zekearneodo/squintan32/altium_libraries/Microdrive_Drive/3d_footprints/sql-rv-1.8-6-body.STEP

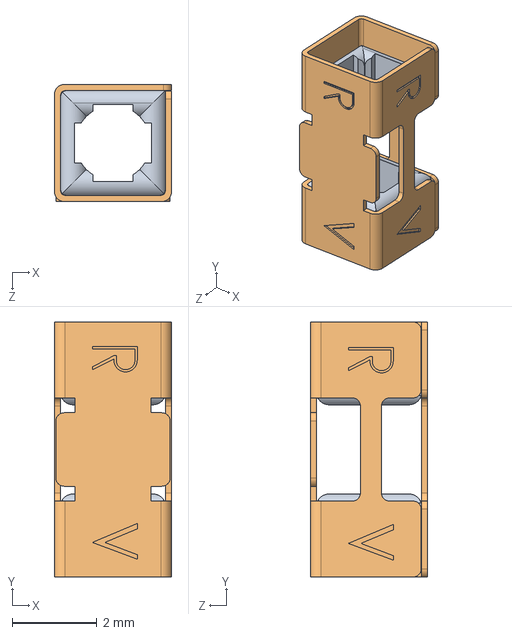
[picture p12: CAD file, 2020-01-03]
altium_libraries/Microdrive_Drive/3d_footprints/sql-rv-1.8-6-body.STEP
2.77 x 6.02 x 2.77 mm
02559-0-0000_WRAPPED x 2
02915-0-0000_Correct Wrap
