zekearneodo/squintan32/altium_libraries/RHD2000_eval_board/3dmodels/pcb_connector_852-10-036-20-001101.stp

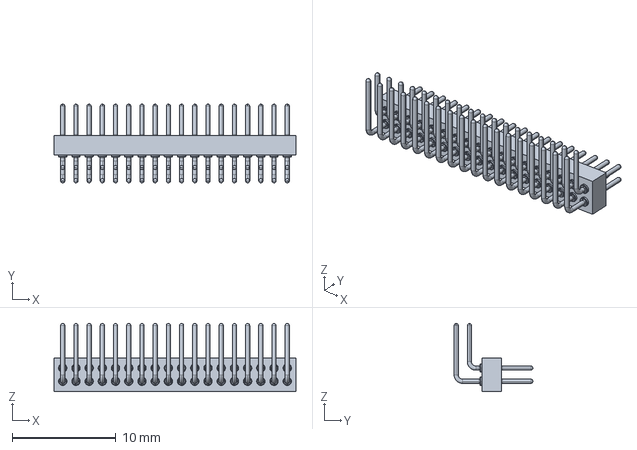
[picture p13: CAD file, 2020-01-03]
altium_libraries/RHD2000_eval_board/3dmodels/pcb_connector_852-10-036-20-001101.stp
23.3 x 7.58 x 6.55 mm
