zekearneodo/squintan32/rev_1_mechanic/pcstl/rhd_board_rev1_right_rules_copy.step

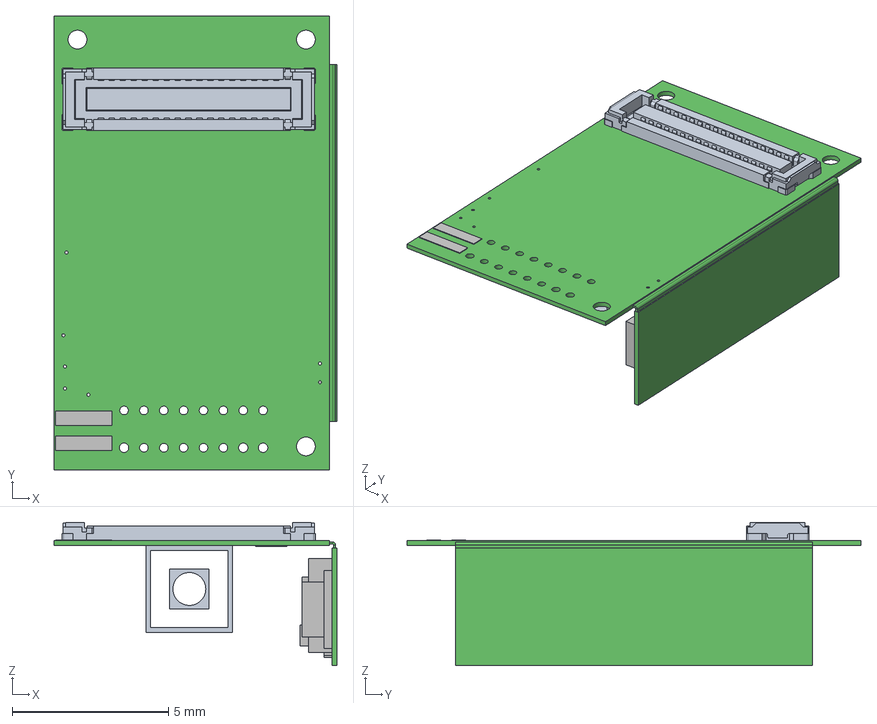
[picture p14: CAD file, 2020-01-03]
rev_1_mechanic/pcstl/rhd_board_rev1_right_rules_copy.step
9.04 x 14.5 x 4.57 mm
Board
sql-rv-1.8-6-12_nc
Extruded x 49
