zekearneodo/squintan32/rev_1_mechanic/stl/shuttle_female_slider.STEP

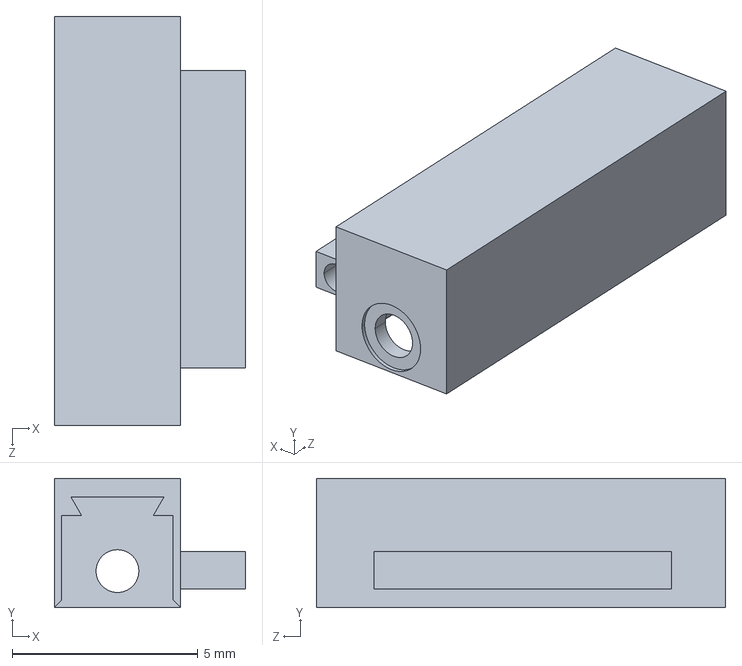
[picture p15: CAD file, 2020-01-03]
rev_1_mechanic/stl/shuttle_female_slider.STEP
5.15 x 3.47 x 11.0 mm
