zekearneodo/squintan32/rhd2132_with_squiggle_logic/mechanical/board_rev0.SLDPRT

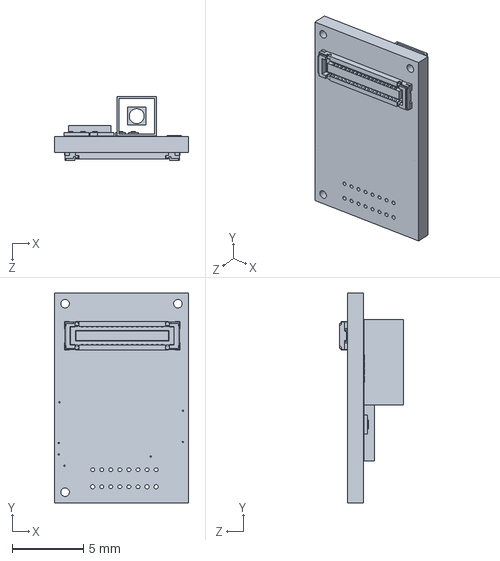
[picture p16: CAD file, 2020-01-03]
rhd2132_with_squiggle_logic/mechanical/board_rev0.SLDPRT
9.40 x 14.7 x 4.50 mm
