zekearneodo/squintan32/rhd2132_with_squiggle_logic/mechanical/rev_1/board_rv1.SLDPRT

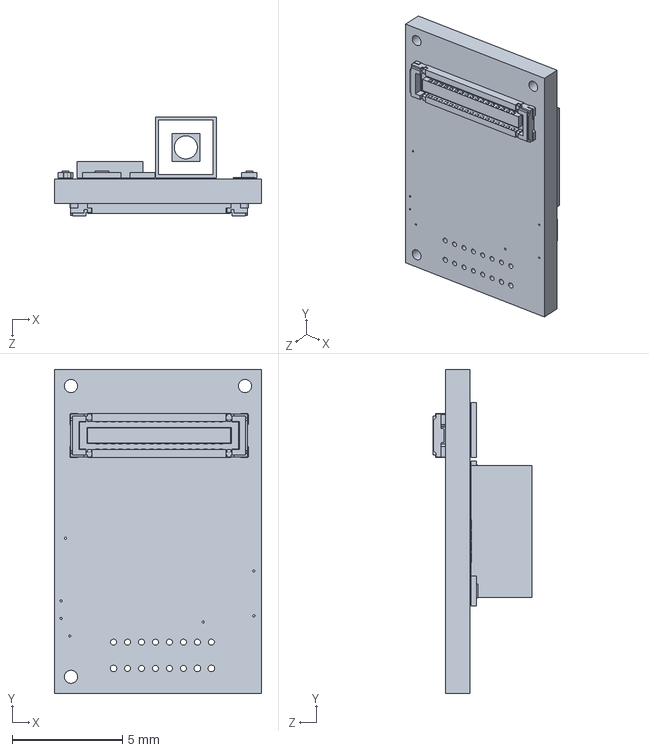
[picture p17: CAD file, 2020-01-03]
rhd2132_with_squiggle_logic/mechanical/rev_1/board_rv1.SLDPRT
9.40 x 14.7 x 4.50 mm
