zekearneodo/squintan32/rhd2132_with_squiggle_logic/Project Outputs for rhd_board/K111027/ExportSTEP/rhd_board_rev1_2.step

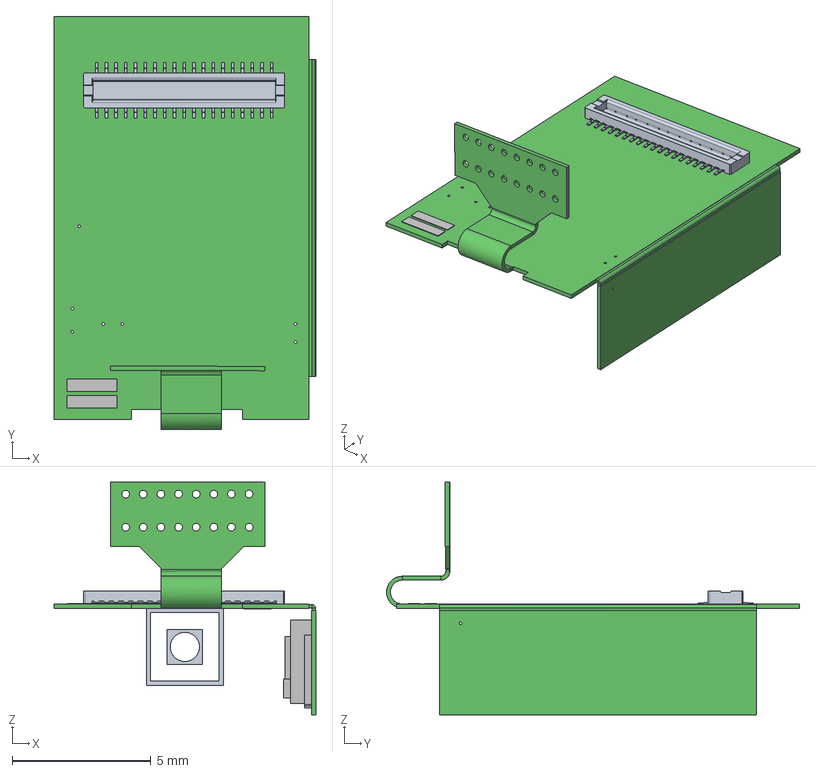
[picture p18: CAD file, 2020-01-03]
rhd2132_with_squiggle_logic/Project Outputs for rhd_board/K111027/ExportSTEP/rhd_board_rev1_2.step
9.43 x 14.9 x 8.38 mm
Board
sql-rv-1.8-6-12_nc
Extruded x 48
