zekearneodo/squintan32/rev_1_mechanic/pcstl/rhd_board_rev1_right_ruless_375hallpy.SLDPRT

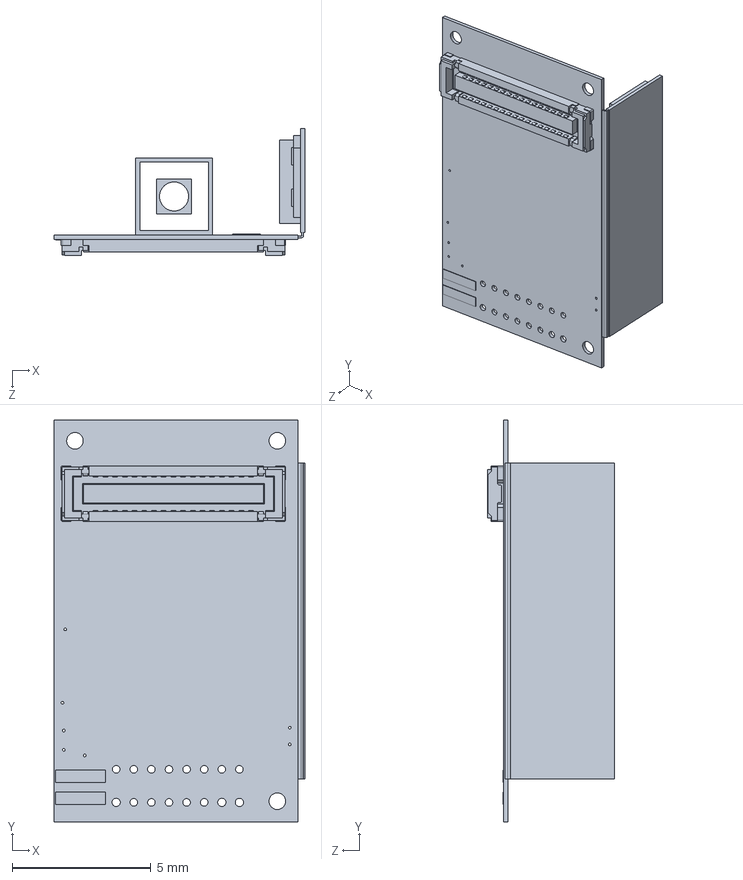
[picture p19: CAD file, 2020-01-03]
rev_1_mechanic/pcstl/rhd_board_rev1_right_ruless_375hallpy.SLDPRT
9.04 x 14.5 x 4.57 mm
