zekearneodo/squintan32/rev_1_mechanic/stl/frame.STEP

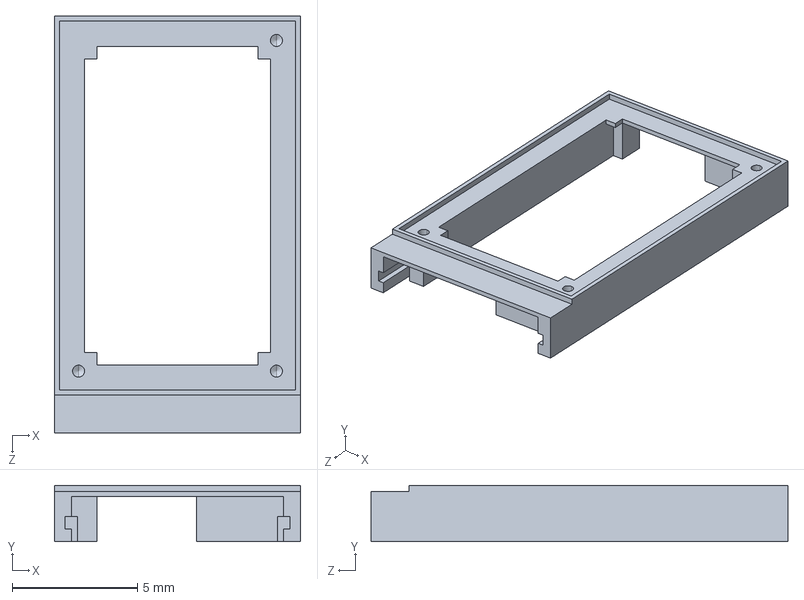
[picture p20: CAD file, 2020-01-03]
rev_1_mechanic/stl/frame.STEP
9.82 x 2.25 x 16.6 mm
