zekearneodo/squintan32/rev_1_mechanic/stl/derived_slider_female.STEP

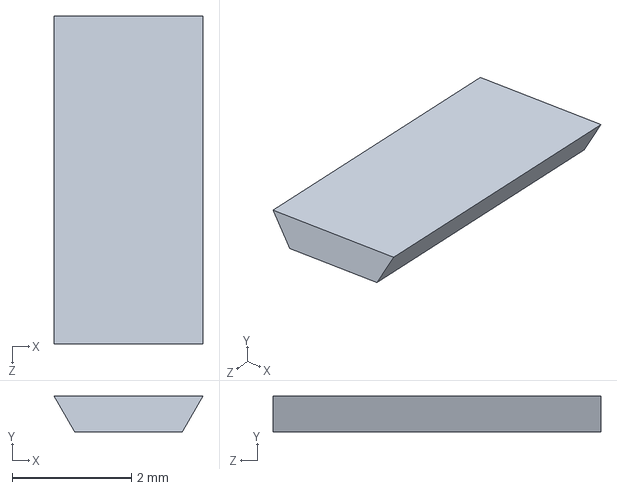
[picture p21: CAD file, 2020-01-03]
rev_1_mechanic/stl/derived_slider_female.STEP
2.50 x 0.6 x 5.50 mm
