zekearneodo/squintan32/rhd2132_with_squiggle_logic/mechanical/rhd_board_rev1.step

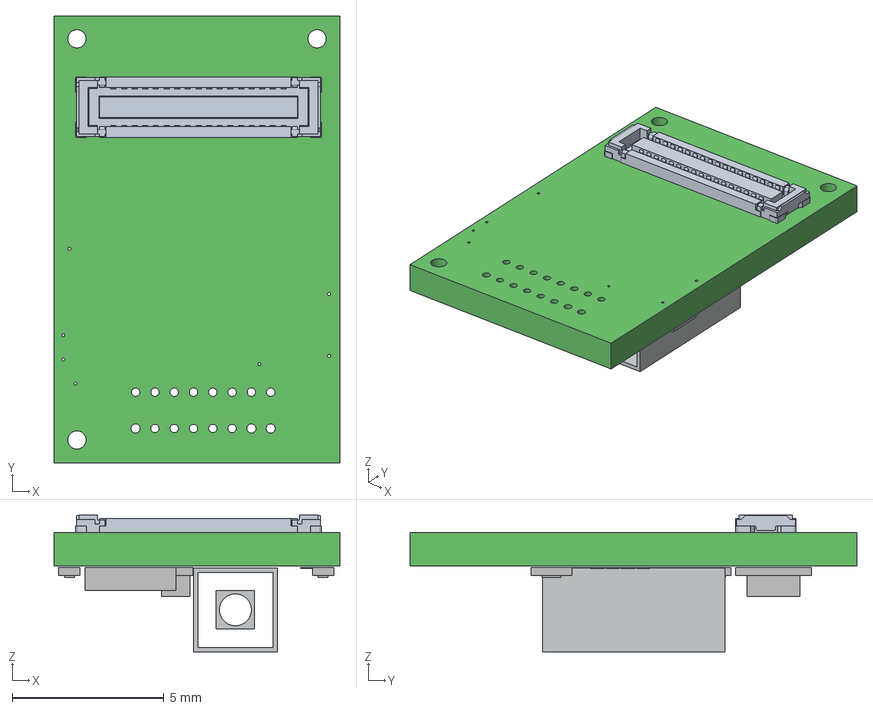
[picture p22: CAD file, 2020-01-03]
rhd2132_with_squiggle_logic/mechanical/rhd_board_rev1.step
9.40 x 14.7 x 4.50 mm
Board
piezo_actuator x 2
Extruded x 47
PS-
PS+
C1
