zekearneodo/squintan32/rev_1_mechanic/stl/shuttle_cap.STEP

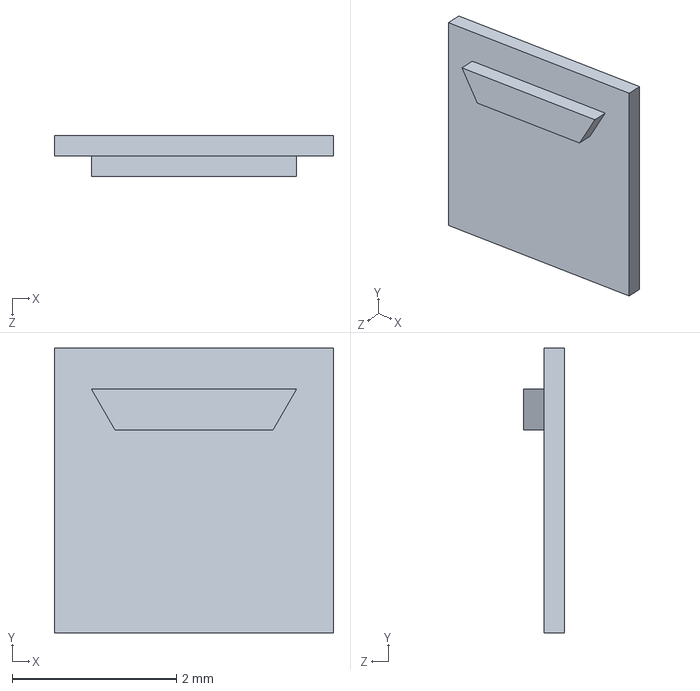
[picture p23: CAD file, 2020-01-03]
rev_1_mechanic/stl/shuttle_cap.STEP
3.40 x 3.47 x 0.5 mm
