zekearneodo/squintan32/altium_libraries/Microdrive_Drive/3d_footprints/sql-rv-1.8-6-12_nc.STEP

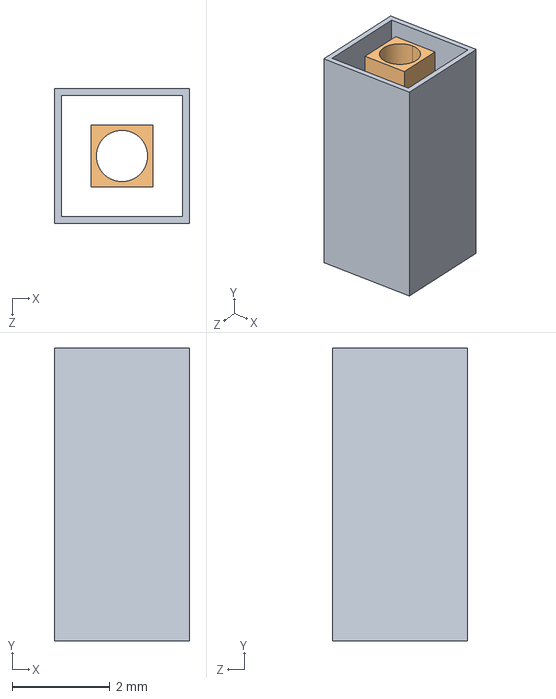
[picture p25: CAD file, 2020-01-03]
altium_libraries/Microdrive_Drive/3d_footprints/sql-rv-1.8-6-12_nc.STEP
2.77 x 6.00 x 2.77 mm
