zekearneodo/squintan32/rev_1_mechanic/stl/case.STEP

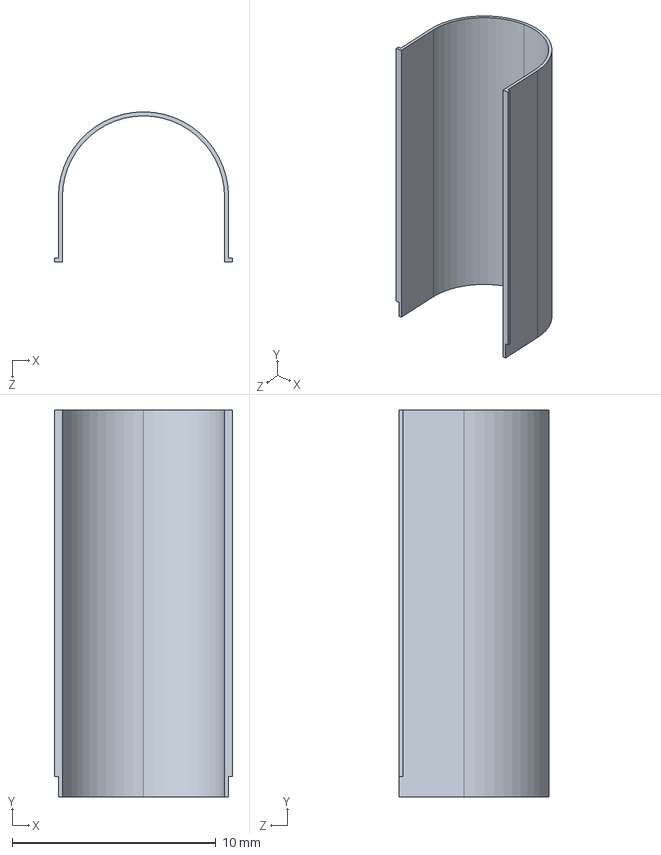
[picture p26: CAD file, 2020-01-03]
rev_1_mechanic/stl/case.STEP
8.76 x 19.0 x 7.38 mm
