zekearneodo/squintan32/rhd2132_with_squiggle_logic/mechanical/omnetics_pzn16_dd.STEP

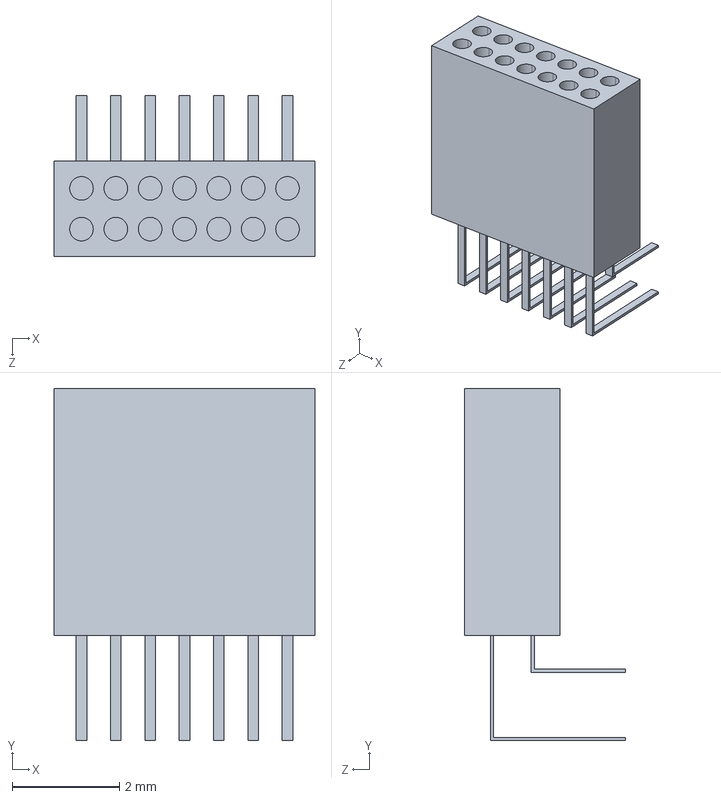
[picture p27: CAD file, 2020-01-03]
rhd2132_with_squiggle_logic/mechanical/omnetics_pzn16_dd.STEP
4.86 x 6.56 x 3.00 mm
