zekearneodo/squintan32/rhd2132_with_squiggle_logic/output_3d_model/board_folded.SLDPRT

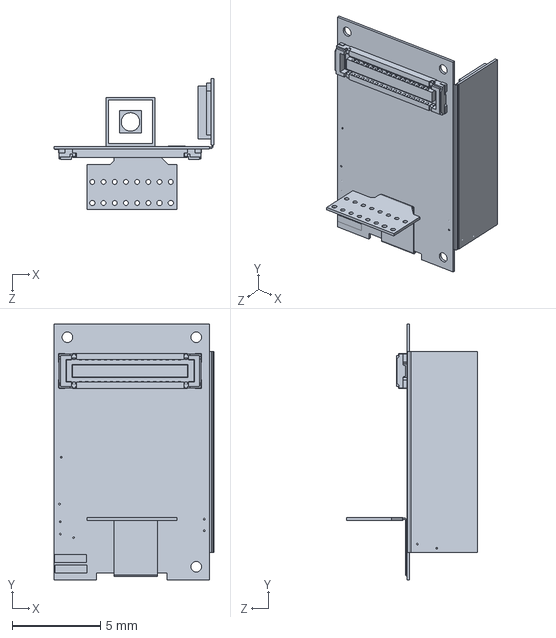
[picture p28: CAD file, 2020-01-03]
rhd2132_with_squiggle_logic/output_3d_model/board_folded.SLDPRT
9.04 x 14.5 x 7.40 mm
