zekearneodo/squintan32/rhd2132_with_squiggle_logic/mechanical/Copy of rhd_board.step

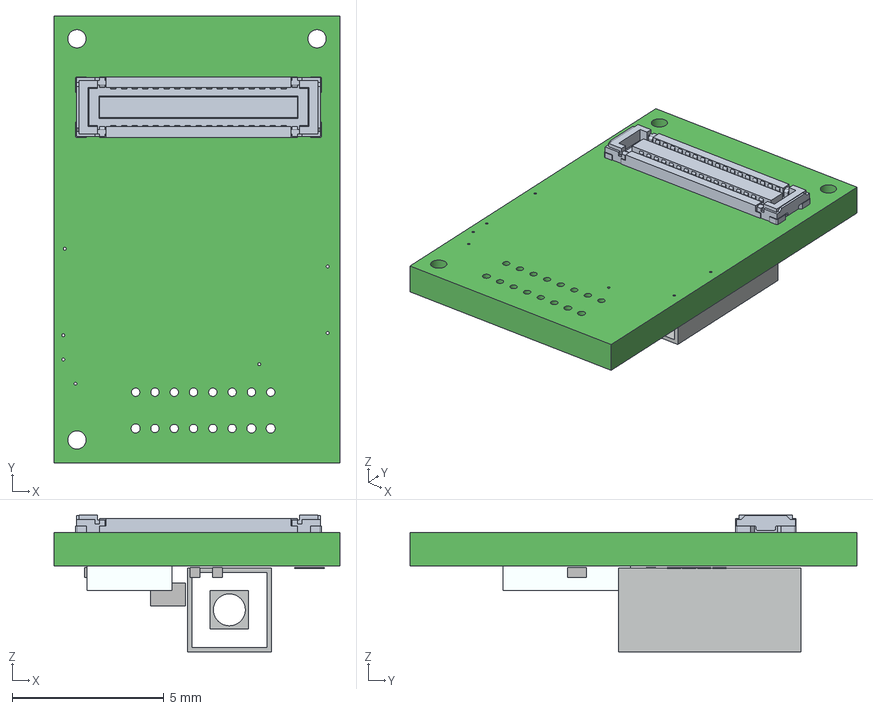
[picture p29: CAD file, 2020-01-03]
rhd2132_with_squiggle_logic/mechanical/Copy of rhd_board.step
9.40 x 14.7 x 4.50 mm
Board
piezo_actuator x 2
Extruded x 13
U0
PS-
PS+
