zekearneodo/squintan32/rev_1_mechanic/cap.SLDPRT

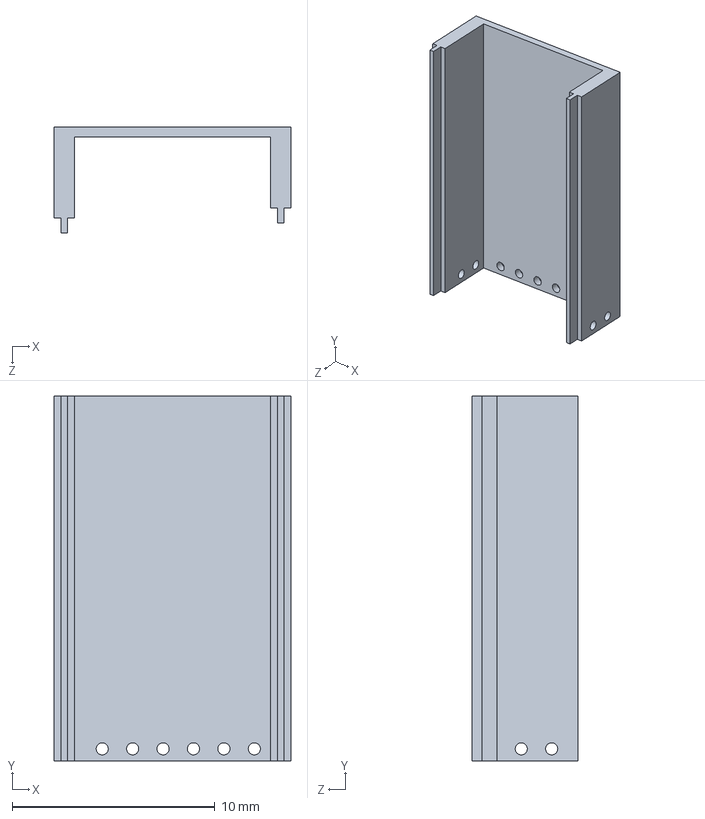
[picture p30: CAD file, 2020-01-03]
rev_1_mechanic/cap.SLDPRT
11.7 x 18.0 x 5.25 mm
