zekearneodo/squintan32/rev_1_mechanic/Magnet_S.SLDPRT

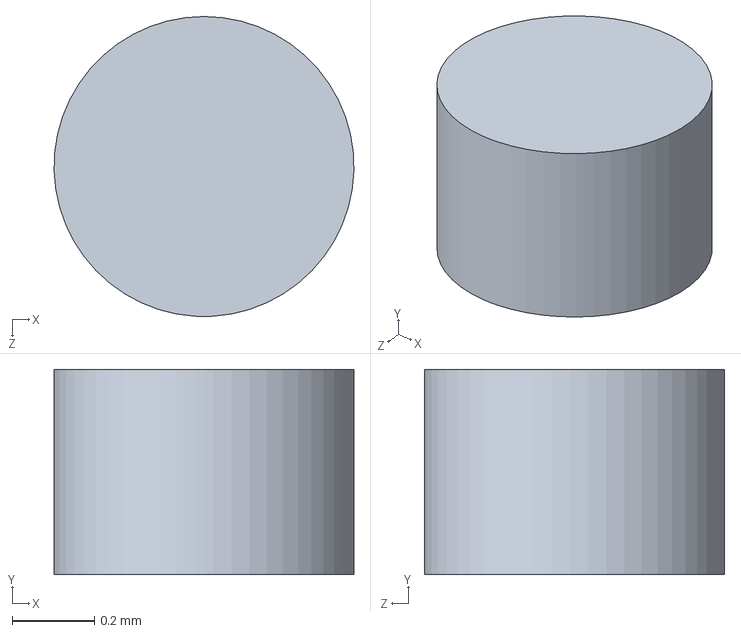
[picture p31: CAD file, 2020-01-03]
rev_1_mechanic/Magnet_S.SLDPRT
0.73 x 0.5 x 0.73 mm
