zekearneodo/squintan32/rev_1_mechanic/slider_derived_male.SLDPRT

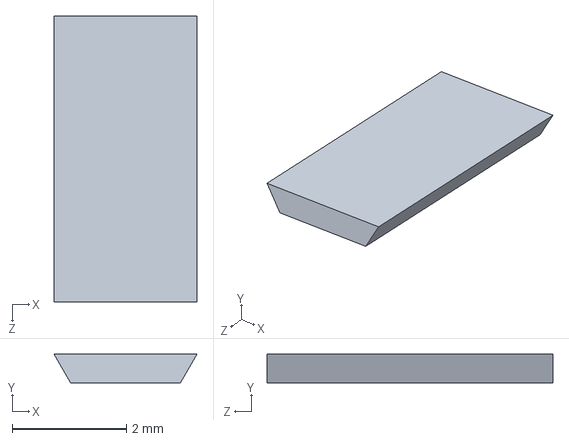
[picture p32: CAD file, 2020-01-03]
rev_1_mechanic/slider_derived_male.SLDPRT
2.50 x 0.5 x 5.00 mm
