zekearneodo/squintan32/rev_1_mechanic/shaft.SLDPRT

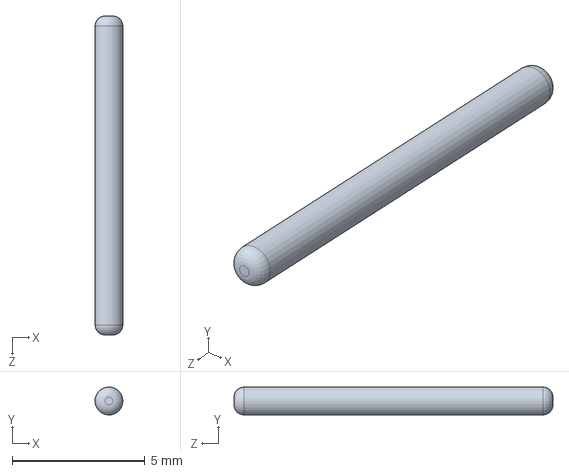
[picture p33: CAD file, 2020-01-03]
rev_1_mechanic/shaft.SLDPRT
1.05 x 1.05 x 12.0 mm
