zekearneodo/squintan32/rev_1_mechanic/derived_slider_male.SLDPRT

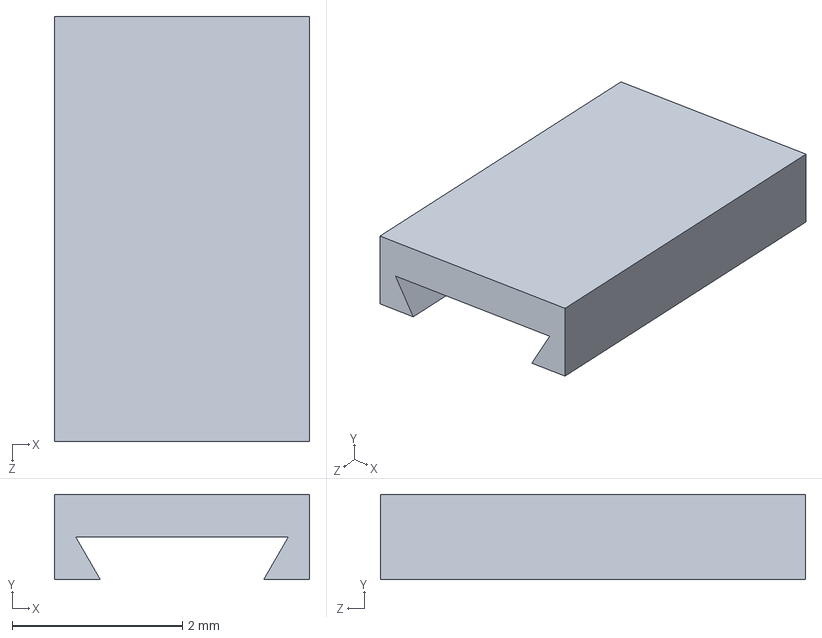
[picture p34: CAD file, 2020-01-03]
rev_1_mechanic/derived_slider_male.SLDPRT
3.00 x 1.00 x 5.00 mm
