zekearneodo/squintan32/rev_1_mechanic/slider_female.SLDPRT

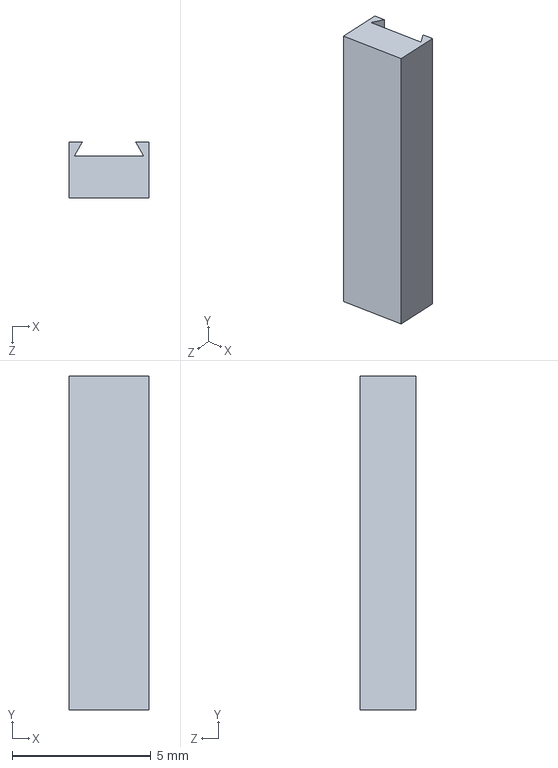
[picture p35: CAD file, 2020-01-03]
rev_1_mechanic/slider_female.SLDPRT
2.87 x 12.0 x 2.00 mm
