zekearneodo/squintan32/rev_1_mechanic/frame_folded_hall.SLDPRT

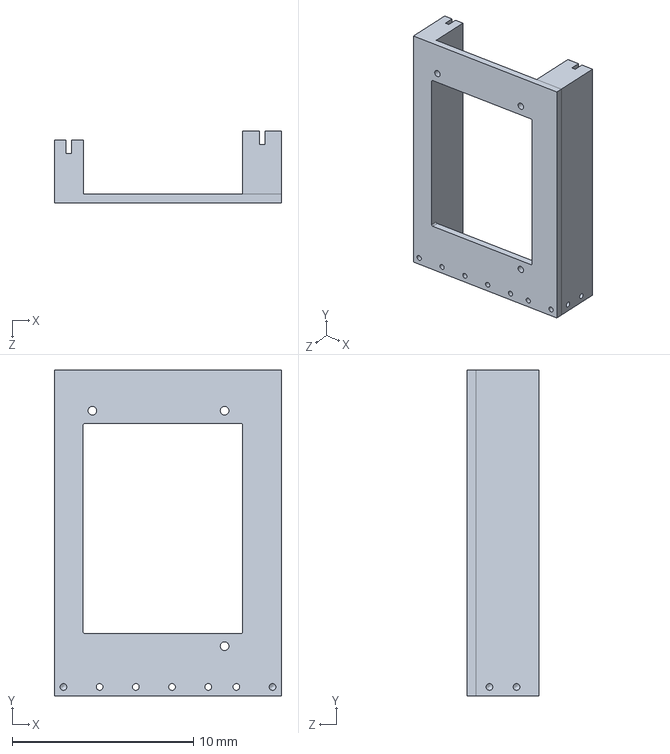
[picture p36: CAD file, 2020-01-03]
rev_1_mechanic/frame_folded_hall.SLDPRT
12.5 x 18.0 x 4.00 mm
