zekearneodo/squintan32/rhd2132_with_squiggle_logic/rhd_board.pdf

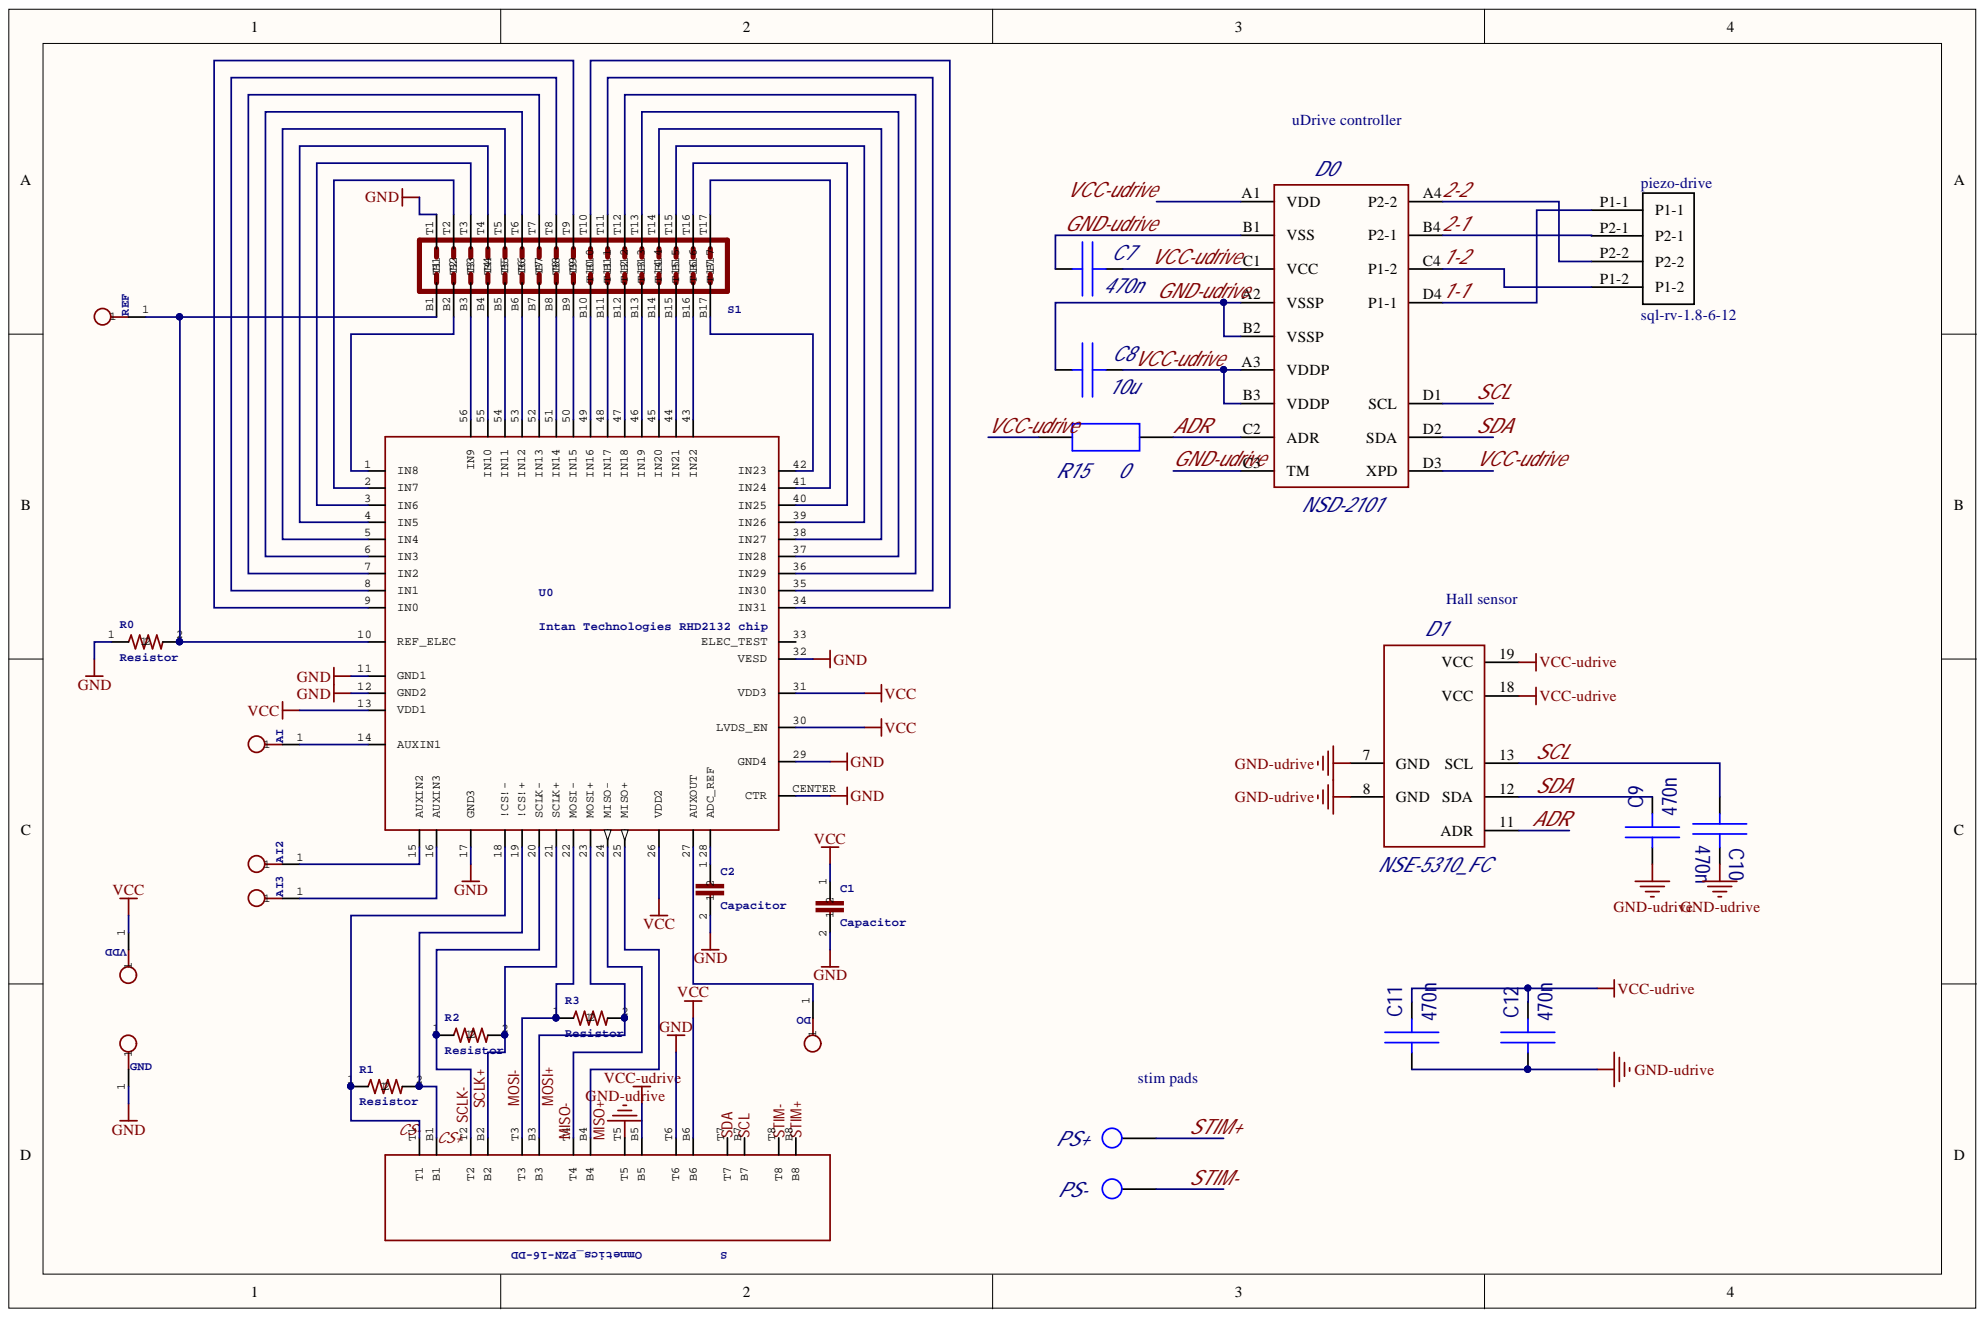
[picture p42: page 1]

VSSP B2

VDDP B3

Intan Technologies RHD2132 chip REF_ELEC 10

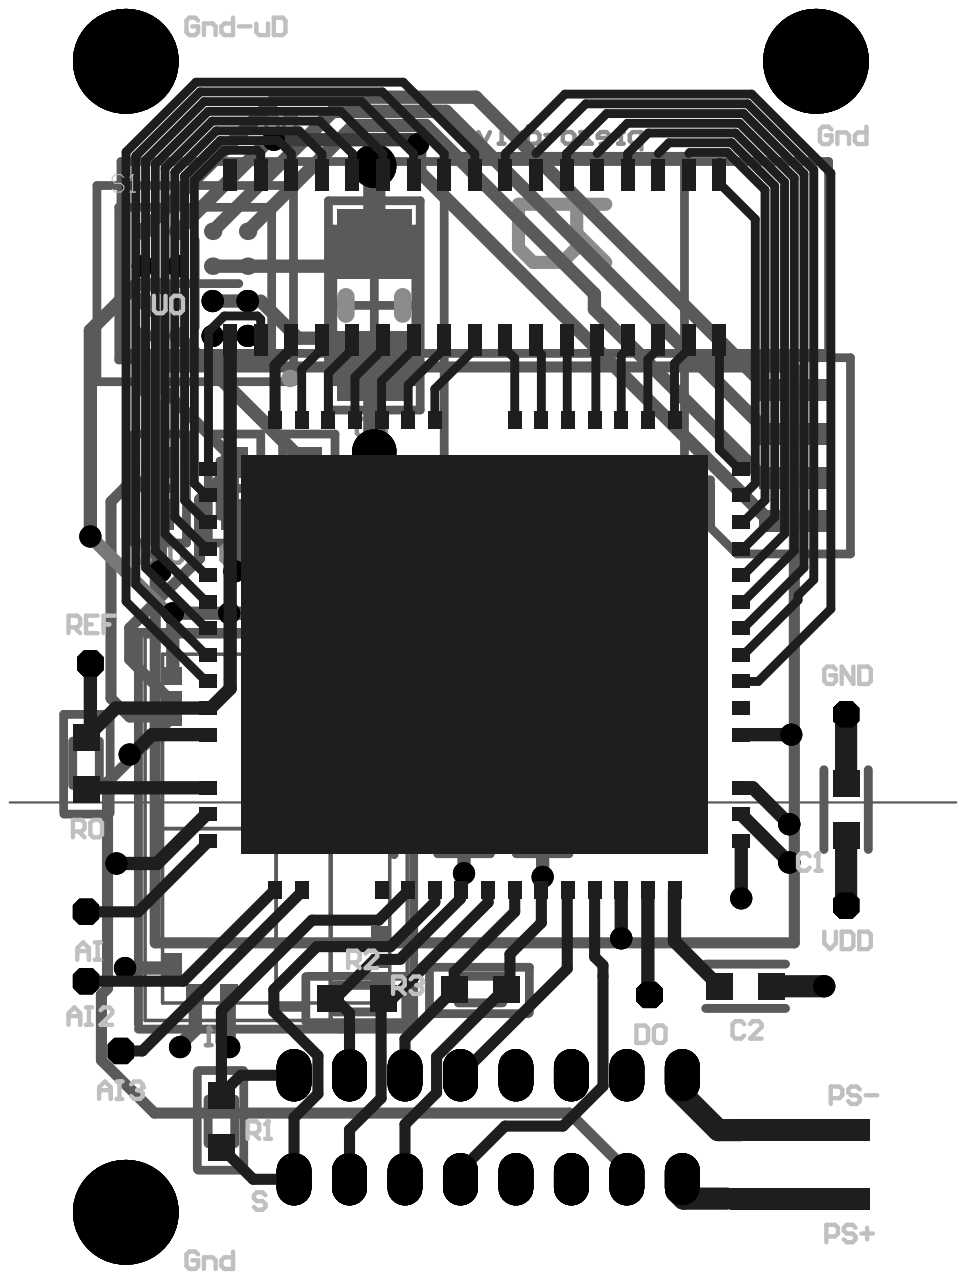
[picture p43: page 2]

# Board S
