zekearneodo/squintan32/rhd2132_with_squiggle_logic/output_3d_model/rhd2132_board_rev1_2_x_t.PDF

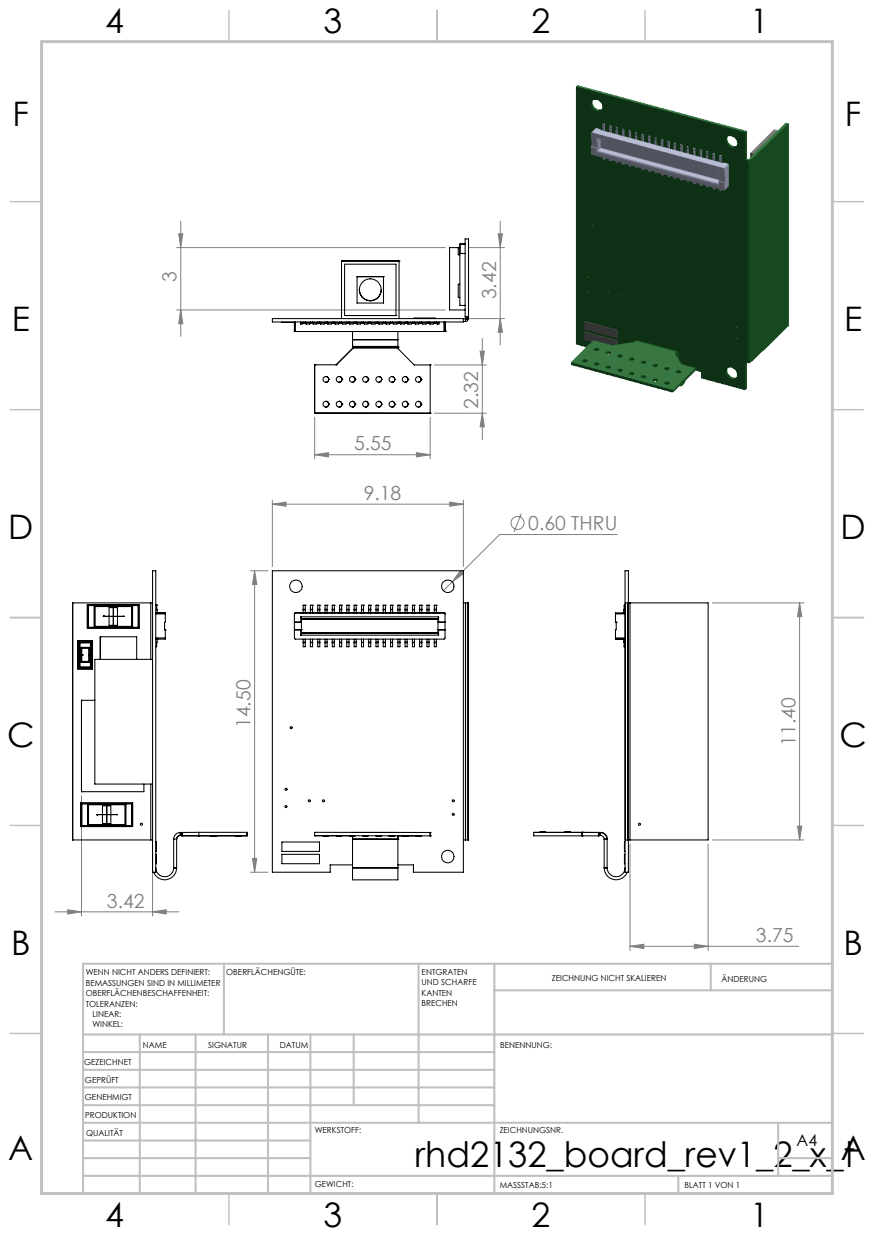
[picture p50: page 1]
0.60 THRU; MASSSTAB:5:1; BLATT 1 VON 1; ZEICHNUNG NICHT SKALIEREN; ÄNDERUNG; UND SCHARFE; WENN NICHT ANDERS DEFINIERT:; OBERFLÄCHENGÜTE:

BEMASSUNGEN SIND IN MILLIMETER
OBERFLÄCHENBESCHAFFENHEIT:
TOLERANZEN:
LINEAR:
WINKEL:

NAME | SIGNATUR | DATUM | | | | BENENNUNG:
QUALITÄT | | | | WERKSTOFF: rhd2132_board_rev1_2_x_t GEWICHT: | ZEICHNUNGSNR. | A4

GEZEICHNET
GEPRÜFT
GENEHMIGT
PRODUKTION
