zekearneodo/squintan32/rhd2132_with_squiggle_logic/Project Outputs for rhd_board/K111027/PDF/rhd_board.PDF

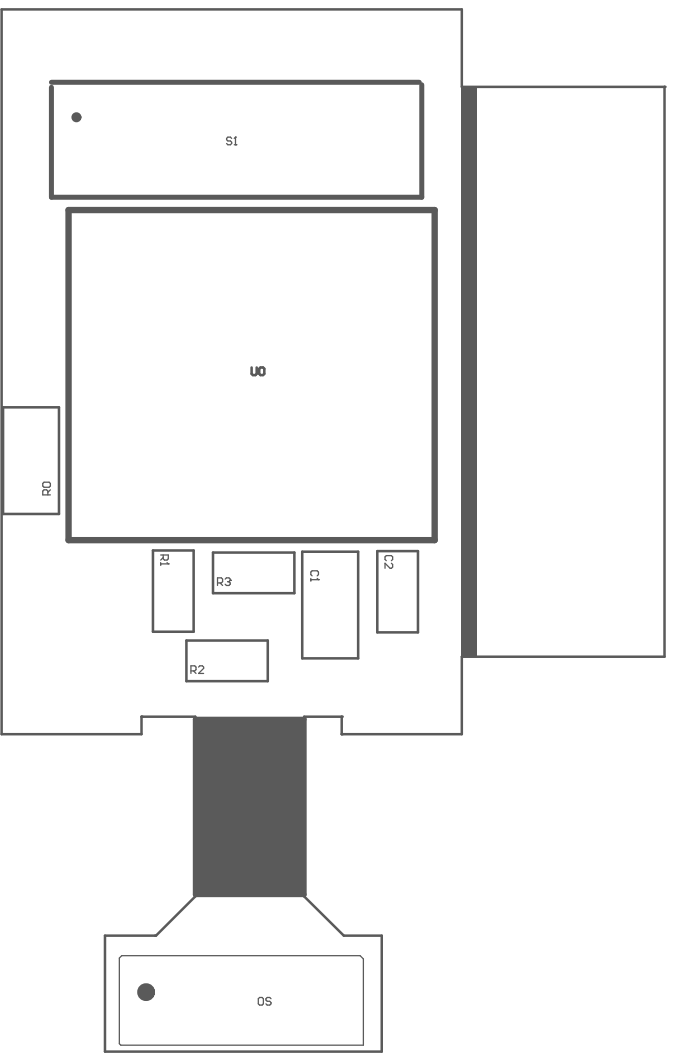
[picture p51: page 1]

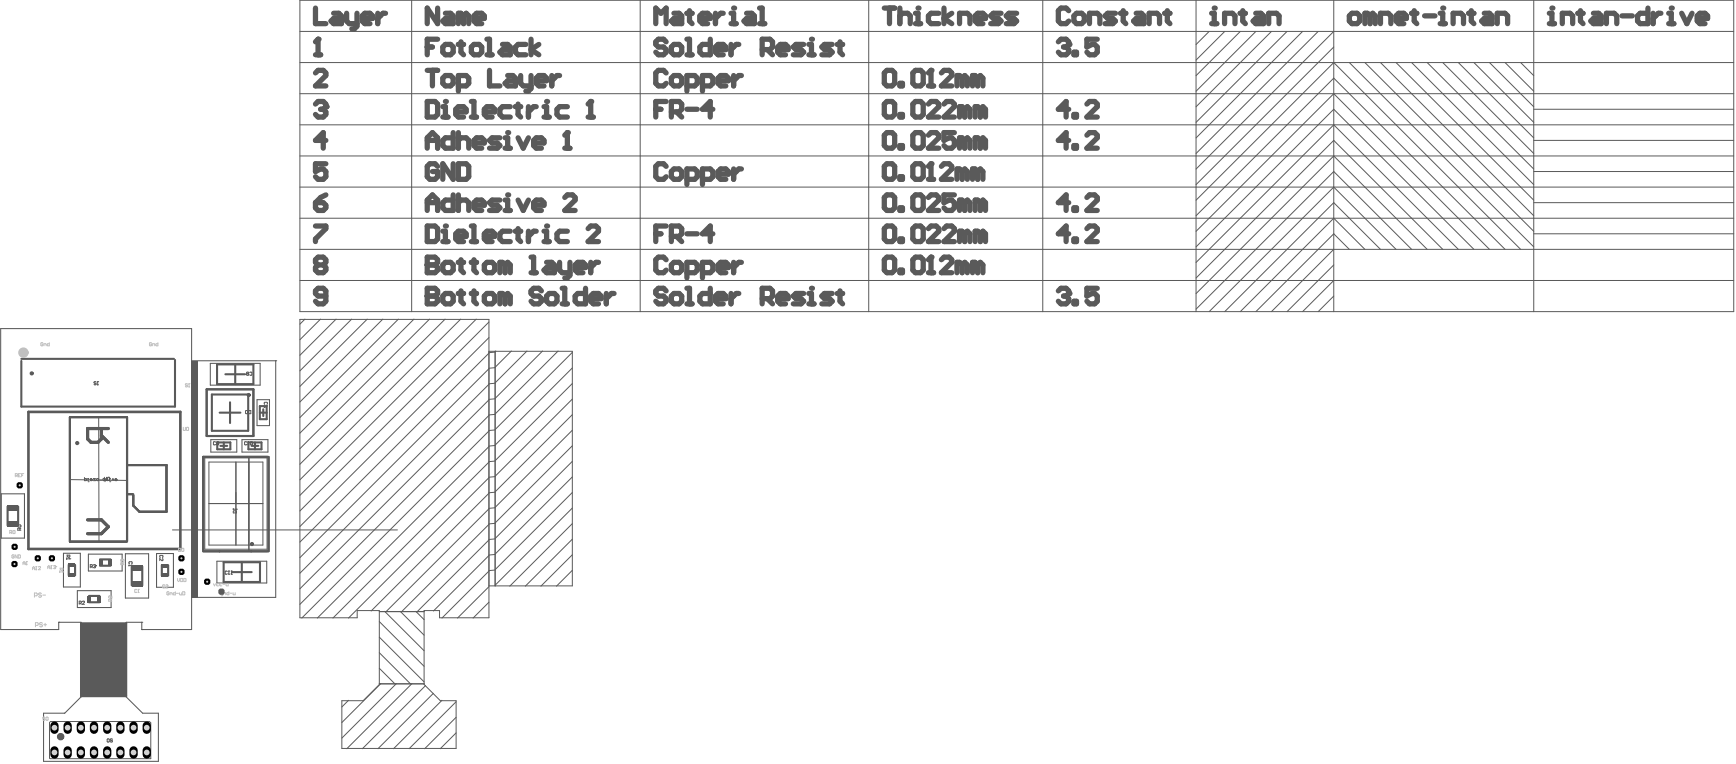
[picture p52: page 2]

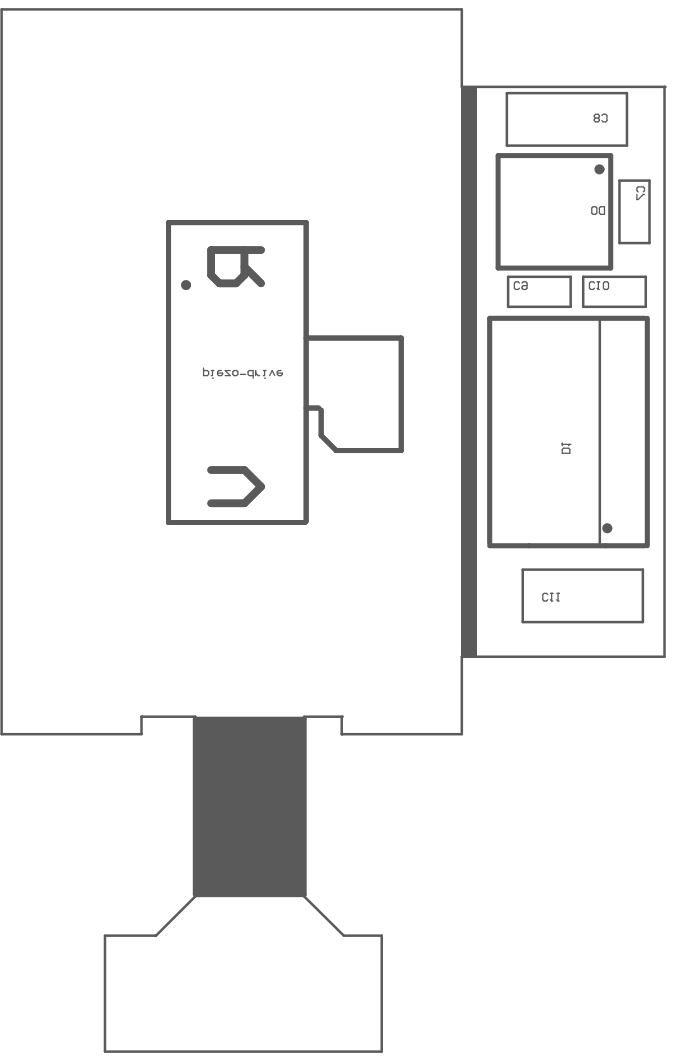
[picture p53: page 3]
